ChloeCrozier/parking_sensor/parking_sensor_demo/ultrasound.cpp

// Park Sharks
// 3.22.2024 V0
// This is a program that functions as an integration test between the ultrasound and radio modules
// I heavily used the RX/TX code we used in class to write this program and I directly used my ultrasound and radio unit test code
// I changed this code to test that a receiving can get a 10 bit representation of the current measured distance and also the state of whether a object is parked or not
// CC1101 Datasheet: https://www.ti.com/lit/ds/symlink/cc1101.pdf?ts=1711001249939&ref_url=https%253A%252F%252Fwww.google.com%252F
// Ultrasound Datasheet: https://media.digikey.com/pdf/Data%20Sheets/Adafruit%20PDFs/4019_Web.pdf
//
// Here are the implementations of the ultrasound class functions from ultrasound.h

#include "ultrasound.h"

// Constructor to intialize the I/O pins and time duration vars
Ultrasound::Ultrasound(int output, int input, int parkingSpaceSize, int detectingCycles) {
  triggerPin = output;
  pinMode(triggerPin, OUTPUT);
  
  echoPin = input;
  pinMode(echoPin,INPUT);

  cycleLength = 1500;
  
  // Shorter times are better for pulseIn() and this is measured in microseconds (us)
  timeSending = 15;
  
  // Parking spaces are around 5 meters (500 cm)
  parkingSpaceDist = parkingSpaceSize;
  
  // Number of measurements needed to determine if the dectected object can be considered as parked
  minDetectionCycles = detectingCycles;
  
  // This var is used to ensure that a spot is only occupied once the object is dectected for n consecutive measurements
  stateCounter = 0;
  
  // Set the parked state to false (no object present long enough to be considered parked)
  parkedState = false;

  // Set the object coutner to 0
  objectCount = 0;

  // Set timeParked to 0
  timeParked = 0;
}

// This is the same method I used in ultrasound_functionality.ino
long Ultrasound::measureTime(void) {
  digitalWrite(triggerPin, LOW);
  delayMicroseconds(2);
  digitalWrite(triggerPin, HIGH);
  delayMicroseconds(timeSending);
  digitalWrite(triggerPin, LOW);
  
  return pulseIn(echoPin, HIGH);
}

// This is the same formula from ultrasound_functionality.ino, but I removed the readInTime part after find better performance with out it
long Ultrasound::measureDist(long duration) {
  return (((duration * 34300) / 2) / 1000000);
}

bool Ultrasound::isValidDist(long distance) {
  // If the distance is out side of the accurate/reasonable datasheet ranges, print what the inaccurate value was
  if ((distance < 2) || (distance > 450)) {
      Serial.print("An inaccurate distance of ");
      Serial.print(distance);
      Serial.println(" was measured. Next cycle starting.");
      return false;
  }
  // If the distance is within an accurate range, print the valid values
  else {
      Serial.print("Distance: ");
      Serial.print(distance);
      Serial.println(" cm");
      return true;
   }
}

// New function that returns true if an object is detected half-way into a parking spot
bool Ultrasound::isOccupied(long distance) {
  // If the object is measured at least half way into the parking spot
  if (distance <= (parkingSpaceDist / 2.0)) {
    Serial.println("State: Occupied");
    return true;
  } else {
    Serial.println("State: Unoccupied");
    return false;
  }
}

// New function that delares an object as parked once it is detected at least minDetectionCycles number of times
void Ultrasound::isParked(long distance) {
  bool occupiedState = isOccupied(distance);
  // If the object has been detected, but not long enough to be parked
  if (occupiedState && !parkedState) {
    stateCounter++;
    if (stateCounter >= minDetectionCycles) {
      stateCounter = 0;
      parkedState = true;
      objectCount++;
      timeParked = millis();
      Serial.print("Car #");
      Serial.print(getObjectCount());
      Serial.println(" has parked");
    }
  }
  // If the detected object has been sensed long enough to be considered parked
  else if (occupiedState && parkedState) {
    Serial.print("Car #");
    Serial.print(getObjectCount());
    Serial.print(" has been parked for ");
    // When printing the time parked, I make sure to include the time of  minDetectionCycles cycles
    Serial.print((getTimeParked() + (minDetectionCycles * (cycleLength))) / 1000.0);
    Serial.println(" seconds");
  }
  // If the object is not detected, but it was previously parked
  else if (!occupiedState && parkedState) {
      Serial.print("Car #");
      Serial.print(getObjectCount());
      Serial.println(" has left the spot");
    parkedState = false;
    // Update time to track time spot is open
    timeParked = millis();
  }
  // If there is no detected object or previously parked car
  else {
//    Serial.println("No change, the spot is still unoccupied");
    stateCounter = 0;
  }
}

// New function that returns the length of the input/output cycle (time between send bursts)
int Ultrasound::getCycleLength(void) {
    return cycleLength;
}

// New function to return the parked state
bool Ultrasound::getParkedState(void) {
    return parkedState;
}

// New function to return the number of objects that have parked
int Ultrasound::getObjectCount(void) {
    return objectCount;
}

// New function that returns the current time minus the time of the last parking state update
long Ultrasound::getTimeParked(void) {
    return (millis() - timeParked);
}

double Ultrasound::getParkingSpaceDist(void) {
  return parkingSpaceDist;
}

int Ultrasound::getMinDetectionCycles(void) {
  return minDetectionCycles;
}

void Ultrasound::setCycleLength(int c) {
  cycleLength = c;
}
